SeraphimlabsLLC/Arch_Bridge/Software/Arch_Bridge/ESP32_rmtdcc.cpp

#ifndef ESP32_RMTDCC_HW_H
  #include "ESP32_rmtdcc.h"
#endif

/* NMRA allows up to 32 bytes per packet, the max length would be 301 bits transmitted and need 38 bytes (3 bits extra). 
 * DCC_EX is limited to only 11 bytes max. Much easier to account for and uses a smaller buffer. 
  */

//Rmtdcc dcc; //Define track channel objects with empty values.
rmt_channel_handle_t rmt_rx_handle = NULL;
rmt_rx_event_callbacks_t* rmt_rx_cbs = NULL; 
rmt_channel_handle_t rmt_tx_handle = NULL;

extern uint64_t time_us;

void Rmtdcc::loop_process() { //Workflow loop
  rmt_rx();
  //rmt_scan(); 

  return;
}
uint8_t Rmtdcc::rmt_rx() {
  rmt_rx_detect = time_us;
  uint8_t bytes_read = 0;
  uint8_t num_bytes = 0;
  uint16_t i = 0;
  uint32_t APB_Div = getApbFrequency() / 1000000; //Reported bus frequency in MHz
  uint8_t rx_size = 0;
  uint32_t word_read = 0;

/*
 //Arduino RMT interface
 if (rmtReceiveCompleted(rx_ch)) { //RMT has data for reading
  //'bool rmtReadAsync(rmt_obj_t*, rmt_data_t*, size_t, void*, bool, uint32_t)'
   rmtReadAsync(rx_ch, rx_rmt_data, rx_data_size, NULL , false, 12); //Populates rx_data with rmt data and rx_data_size with the size of data
   rx_data_size = 1; 
   rmt_data_t* databit = NULL;
 }*/

/*
 //Test Read 
 uint32_t rmt_rx_readptr = REG_GET_FIELD(RMT_CH4STATUS_REG, RMT_APB_MEM_RADDR_CH4);//REG_READ(RMT_CH4STATUS_REG)) & 0x1FF;
 uint32_t rmt_rx_writeptr = REG_GET_FIELD(RMT_CH4STATUS_REG, RMT_MEM_WADDR_EX_CH4);//REG_READ(RMT_CH4STATUS_REG)) &
 if (rmt_rx_writeptr > (192 + 16)) {
  rmt_rx_stop(rmt_channel_t(DIR_MONITOR_RMT));

  rmt_rx_start(rmt_channel_t(DIR_MONITOR_RMT), true); 
 }
 Serial.printf("RMT_RX read pointer = %u, write pointer = %u \n",rmt_rx_readptr, rmt_rx_writeptr);
*/ 
/* 
//  volatile rmt_item32_t* item;
//  item = RMTMEM.chan[DIR_MONITOR_RMT].data32;
//  std::cout << "item d0: " << (item->duration0 / APB_Div) << " L0: " << item->level0  << " d1: " << (item->duration1 / APB_Div)  << " :L1: " << item->level1  << std::endl;
//Serial.printf("item duration: %u, item level0: %u, item duration1: %u, item level1: %u \n", (item->duration0 / APB_Div), item->level0, (item->duration1 / APB_Div), item->level1);  

   time_us = TIME_US;
   if ((time_us - last_rmt_read) < (DCC_0_HALFPERIOD * 8)) {
    return 0; 
   }
   
   if (*rx_data_size > 0) { //* is dereference, to get the value contained in the pointer
     Serial.printf("rmt_rx_data contained %u items \n", *rx_data_size); 
   }

   //Direct RMT RX read
   uint32_t rxtest = REG_READ(RMT_CH4DATA_REG); 
   if (rxtest > 0) {
     Serial.printf("RMT_RX contained value %u \n", rxtest); 
   }

  rmt_item32_t databit;
  int dur_delta = 0;
  int8_t bitzero = -1;
  int8_t bitone = -1;
  
  //while (rx_rmt_data[i] != NULL) {
  while (i < 32){
   if (!&rx_rmt_data[i]) { //Avoids crash if no data returned. 
    return 0; 
   }
   databit = rx_rmt_data[i];
   
   //Straightforward decoding when the RMT is in-phase with it and 1 symbol = 1 bit. 
   if ((databit.duration0 > DCC_1_MIN_HALFPERIOD) && (databit.duration0 < DCC_1_MAX_HALFPERIOD)) {
      bitzero = 1; 
   }
   if ((databit.duration0 > DCC_0_MIN_HALFPERIOD) && (databit.duration0 < DCC_0_MAX_HALFPERIOD)) {
      bitzero = 0; 
   }
   if ((databit.duration1 > DCC_1_MIN_HALFPERIOD) && (databit.duration1 < DCC_1_MAX_HALFPERIOD)) {
      bitone = 1; 
   }
   if ((databit.duration1 > DCC_0_MIN_HALFPERIOD) && (databit.duration1 < DCC_0_MAX_HALFPERIOD)) {
      bitone = 0; 
   } 
   dur_delta = databit.duration0 - databit.duration1;
   
   if ((bitzero != bitone) && (bitzero > -1) && (bitone > -1)) { //Halves don't match, but both have valid times. Use rx_last_bit duration1 as bitone.  
/*     //Find some other way to validate
       //if (!(rx_last_bit)) { //Haven't seen any bits prior. Go to the next bit.
      //continue; 
    // } 
     
     if ((rx_last_bit.duration1 > DCC_1_MIN_HALFPERIOD) && (rx_last_bit.duration1 < DCC_1_MAX_HALFPERIOD)) {
       bitone = 1; 
     }
     if ((rx_last_bit.duration1 > DCC_0_MIN_HALFPERIOD) && (rx_last_bit.duration1 < DCC_0_MAX_HALFPERIOD)) {
       bitone = 0; 
     } 
     dur_delta = databit.duration0 - rx_last_bit.duration1; 
   }
   if ((bitzero + bitone == 0) || ((bitzero + bitone == 2) && ((dur_delta > -6) && (dur_delta < 6)))){ 
    //Both bits 0 or both bits 1 && both halves of 1 within 6uS
       //rx_bit_processor(bitzero); //Process the bits into packet
   } else { //Invalid bit. Drop the bit and try again. 
     rx_byteout = 0; 
     rx_num_bits = 0; 
   }

   rx_last_bit = rx_rmt_data[i]; //Store the symbol we just decoded for the next cycle in case of a phase straddle
   i++;
  }
  
  //vRingbufferReturnItem(rmt_rx_handle, (void*) dcc_items); //Free up space in the rmt_rx ring 
  //rmt_memory_rw_rst(rmt_channel_t (DIR_MONITOR_RMT));
  return num_bytes;
  */
} 

/*
void IRAM_ATTR rmt_isr_handler(void* arg){
  //read RMT interrupt status.
  uint32_t intr_st = RMT.int_st.val;

//  if (intr_st && ch4_rx_thr_event_int_raw){
//    std::cout << "RMT CH4 Threshold event"; 
//  }
    
  
  RMT.conf_ch[DIR_MONITOR_RMT].conf1.rx_en = 0;
  RMT.conf_ch[DIR_MONITOR_RMT].conf1.mem_owner = RMT_MEM_OWNER_TX;
  volatile rmt_item32_t* item = RMTMEM.chan[DIR_MONITOR_RMT].data32;
  if (item) Serial.print ((item)->duration0);
  
//  RMT.conf_ch[DIR_MONITOR_RMT].conf1.mem_wr_rst = 1;
//  RMT.conf_ch[DIR_MONITOR_RMT].conf1.mem_owner = RMT_MEM_OWNER_RX;
//  RMT.conf_ch[DIR_MONITOR_RMT].conf1.rx_en = 1;

  //clear RMT interrupt status.
  RMT.int_clr.val = intr_st;
}
*/ 

void Rmtdcc::rmt_rx_init(){ 
  esp_err_t res ;
  //rx_ch = NULL; 
  bool rmt_recv = false;
  //Serial.printf("RMT_RX Initialized \n");

  Serial.printf("RMT RX: Configuring DIR_MONITOR input on %u \n", DIR_MONITOR);
  gpio_reset_pin(gpio_num_t(DIR_MONITOR));
  gpio_set_direction(gpio_num_t(DIR_MONITOR), GPIO_MODE_INPUT);
  gpio_set_pull_mode(gpio_num_t(DIR_MONITOR), GPIO_FLOATING); 

/* Arduino Library 
//bool rmtInit(int pin, rmt_ch_dir_t channel_direction, rmt_reserve_memsize_t memsize, uint32_t frequency_Hz);
//bool rmtInit(int DIR_MONITOR, rmt_ch_dir_t channel_direction, rmt_reserve_memsize_t memsize, uint32_t frequency_Hz);
rmt_recv = rmtInit(DIR_MONITOR, RMT_RX_MODE, RMT_MEM_192);

  if (rmt_recv == false) {
    Serial.printf("Failed to initialize RMT Reciver using Arduino interface \n");
  }
  return;
}*/

  // Configure the RMT channel for RX to audit incoming DCC
  //Using IDF 4.4.6 interface. Arduino doesn't seem to support 5.1 as of November 2023.
/*  uint32_t APB_Div = getApbFrequency() / 1000000; //Reported bus frequency in MHz
  rmt_config_t rmt_rx_config = {                                           
    .rmt_mode = RMT_MODE_RX,                
    .channel = rmt_channel_t(DIR_MONITOR_RMT),                  
    .gpio_num = gpio_num_t(DIR_MONITOR),                       
    .clk_div = APB_Div,       
    .mem_block_num = 1,                   
    .flags = 0,                             
    .rx_config = {                                              
      .idle_threshold = ((DCC_0_MAX_HALFPERIOD + 2) * APB_Div), //RMT Idle timeout  
      .filter_ticks_thresh = 255, //Glitch filter has max allowed of 255 ticks  
      .filter_en = true,                  
    }                                       
  }; */

//Arduino ESP32 core 3 aka IDF 5.1 API:

  rmt_receive_config_t rx_config = {
    .signal_range_min_ns = 25000,
    .signal_range_max_ns = 1000000,
  };   
//    .extra_flags.en_partial_rx = 1, //Trips complete ISR when buffer is at half 
  
  rmt_rx_channel_config_t* rx_ch_conf = NULL;
  rx_ch_conf = new rmt_rx_channel_config_t;
  rx_ch_conf->gpio_num = gpio_num_t(DIR_MONITOR);
  rx_ch_conf->clk_src = RMT_CLK_SRC_DEFAULT;
  rx_ch_conf->resolution_hz = 1000000;         //1MHz, so 1uS per tick
  rx_ch_conf->mem_block_symbols = 64;          //4 bytes per block, so 256 bytes  };
  /*
    .flags.invert_in = false,
    .flags.with_dma = false, 
    .flags.io_loop_back = false,
    .intr_priority = 0,
  }; */
  
//res = ESP_ERROR_CHECK(rmt_new_rx_channel(rx_ch_conf, rmt_rx_handle));
if (!(res == ESP_OK)) {
  Serial.printf("RMT RX: Error initializing handle \n"); 
}

  rmt_rx_cbs = new rmt_rx_event_callbacks_t;
  rmt_rx_cbs->on_recv_done = rmt_rx_done_callback_t(rmt_rx_done);
//  res = ESP_ERROR_CHECK(rmt_rx_register_event_callbacks(rmt_rx_handle, rmt_rx_cbs, NULL));

/*If possible configure:
* RMT_MEM_RX_WRAP_EN_CHm so it reads in a loop. 
* RMT_CHm_RX_LIM_REG set the number of RX entries before threshold interrupt
* RMT_CHm_RX_THR_EVENT_INT_RAW(m = 4-7)  so that it interrupts on RX_LIM_REG instead of full
 */

/*
//  ESP_ERROR_CHECK(rmt_config(&rmt_rx_config));
//  ESP_ERROR_CHECK(rmt_set_memory_owner(rmt_channel_t(DIR_MONITOR_RMT), rmt_mem_owner_t (1))); //Set RMT RX memory owner
  REG_WRITE(RMT_CH4_RX_LIM_REG, 1); //Trigger RX Threshold ISR at 1 symbol
  
  REG_SET_BIT(RMT_CH4CONF0_REG, 24); //Enable manual register changes
  REG_SET_BIT(RMT_CH4CONF1_REG, 13); //Enable RX Wrap
    Serial.printf("RMT_CH4 RX Wrap = %u \n", REG_GET_BIT(RMT_CH4CONF1_REG, 13));
//  REG_CLEAR_BIT(RMT_MEM_RX_WRAP_EN_CH4, 0);  
//  ESP_ERROR_CHECK(rmt_isr_register(rmt_isr_handler, NULL, 0, NULL));
//  ESP_ERROR_CHECK(rmt_driver_install(rmt_rx_config.channel, 256, ESP_INTR_FLAG_LOWMED|ESP_INTR_FLAG_SHARED));  
//  ESP_ERROR_CHECK(rmt_get_ringbuf_handle(rmt_channel_t(DIR_MONITOR_RMT), &rmt_rx_handle)); //Ring buffer handle
//  ESP_ERROR_CHECK(rmt_rx_start(rmt_channel_t(DIR_MONITOR_RMT), true)); //Enable RMT RX, true to erase existing RX data
  Serial.printf("RMT_APB_FIFO_MASK = %u \n", REG_GET_FIELD(RMT_SYS_CONF_REG, RMT_APB_FIFO_MASK)); //Check if FIFO or addr+offset read mode
  Serial.printf("RMT_CH4_READ = %u \n",REG_READ(RMT_CH4DATA_REG));  

//If necessary to change GPIO assignments
//esp_err_t rmt_set_gpio(rmt_channel_t channel, rmt_mode_t mode, gpio_num_t gpio_num, bool invert_signal)
 
  Serial.printf("RMT_RX DCC Auditing Initialized using buffer handle %d \n", rmt_rx_handle); 
  return;
  */
}

#if DCC_GENERATE == true 
    //Initialize RMT for DCC TX 
void Rmtdcc::rmt_tx_init(){
/*  uint32_t APB_Div = getApbFrequency() / 1000000;
  rmt_config_t rmt_tx_config;
  // Configure the RMT channel for TX
  rmt_tx_config.rmt_mode = RMT_MODE_TX;
  rmt_tx_config.channel = rmt_channel_t(DIR_OVERRIDE_RMT);
  rmt_tx_config.clk_div = APB_Div; //Multiplier is now dynamic based on reported APB bus frequency. 
  rmt_tx_config.gpio_num = gpio_num_t(DIR_OVERRIDE);
  rmt_tx_config.mem_block_num = 4; // With longest DCC packet 11 inc checksum (future expansion)
                            // number of bits needed is 22preamble + start +
                            // 11*9 + extrazero + EOT = 124
                            // 2 mem block of 64 RMT items should be enough
//  ESP_ERROR_CHECK(rmt_config(&rmt_tx_config));
  // NOTE: ESP_INTR_FLAG_IRAM is *NOT* included in this bitmask
//  ESP_ERROR_CHECK(rmt_driver_install(rmt_tx_config.channel, 0, ESP_INTR_FLAG_LOWMED|ESP_INTR_FLAG_SHARED));    
*/
  Serial.printf("RMT_TX DCC Test Signal Initialized\n"); 
  return;
}
/*
//From DCC-EX ESP32 branch DCCRMT.cpp. 
void Rmtdcc::setDCCBit1(rmt_item32_t* item) {
  item->level0    = 1;
  item->duration0 = DCC_1_HALFPERIOD;
  item->level1    = 0;
  item->duration1 = DCC_1_HALFPERIOD;
}

void Rmtdcc::setDCCBit0(rmt_item32_t* item) {
  item->level0    = 1;
  item->duration0 = DCC_0_HALFPERIOD;
  item->level1    = 0
}

void Rmtdcc::setEOT(rmt_item32_t* item) {
  item->val = 0;
}*/

#endif

void IRAM_ATTR rmt_rx_done(){

  return;
}

void rmt_loop() { //Reflector into Rmtdcc::loop_process();
//  dcc.loop_process(); 
}
