SeraphimlabsLLC/Arch_Bridge/Software/Arch_Bridge/ESP32_uart.h

#pragma once
#define ESP32_UART_H

#include "Arduino.h"
#include "driver/gpio.h"
#include "driver/uart.h"
#include "soc/uart_reg.h"

//Use config.h if present, otherwise defaults
#ifndef CONFIG_H
  #if __has_include ("config.h")
    #include "config.h"
  #endif
  #ifndef CONFIG_H
    #include "config.example.h"
  #endif
#endif  

class ESP_Uart {
  public:
  uint8_t uart_num; 
  uint16_t tx_buff; //tx buffer size
  uint16_t rx_buff; //rx buffer size
  uint32_t baud_rate;
  uint8_t uart_mode; //0 = normal, 1 = direct r/w
  char* rx_read_data; //Pointer to the data just read
  uint16_t rx_read_len; //Size of rx_read_data
  uint8_t rx_read_processed; //read status, 0 when new, 255 when fully processed.
  uint8_t tx_write_processed; //write status, 0 when new, 255 when fully processed.
  volatile bool tx_done; //Set to false when putting data in the tx fifo, ISR will set to true again when done. 

  void uart_init(uint8_t uartnum, uint8_t txpin, uint8_t rxpin, uint32_t baudrate, uint16_t txbuff, uint16_t rxbuff);
  uint16_t uart_read(uint8_t readlen); //read the specified number of bytes into rx_read_data
  uint16_t read_len(); //returns how much data there is to be read 
  void uart_write(const char* write_data, uint8_t write_len); //Write to uart up to write_len bytes from write_data
  uint16_t uart_tx_len(); //Fetch how much data is currently in the TX buffer
  void IRAM_ATTR uart_invert(bool tx, bool rx); //Invert UART TX pin
  void uart_tx_int_txdone(bool enabled); //Turn TX Done ISR on and off
  void uart_rx_flush(); //Erase the RX buffer contents
  void rx_flush(); //Reset the rx buffer
  void tx_flush(); //Reset the tx buffer
  //void set_rx_thresh(uint8_t limit); //Maximum 96 bytes 

  //pins must be public for Loconet CD to work. 
  gpio_num_t tx_pin;
  gpio_num_t rx_pin;

  private: 
  uint32_t uart_inv_pinmask; //Stores the last used pinmask


};

void ESP_uart_init();
